obiwanjacobi/zalt2/chats/smart IDE module.md

> This refers to `Zalt\Under Construction\IDE v0.2\readme.md`

This is a **really well-thought-out design**. You've clearly put significant effort into abstracting away the complexity while maintaining practical performance. Let me give you some detailed feedback.

## Overall Architecture

**Strengths:**
- **Clean abstraction** — the Z80 program never deals with IDE timing, sectors, or cluster chains. It just says "read file X" or "write Y bytes"
- **Efficient pipelining** — prefetching the next block while the Z80 processes the current one is smart
- **DMA-driven** — the MCU takes the bus only when needed, minimizing Z80 stalls
- **Flexible addressing** — ContentOffset and ContentLength let you handle partial file reads/writes elegantly
- **Interleaving support** — multiple command blocks means you can juggle several operations

**The design handles real constraints well** — the 4kB MCU buffer limit is acknowledged, and you've built the block-based protocol around it.

---

## Detailed Observations

### Register Design

Your register set is minimal and clean. A few thoughts:

**Buffer Address and Command Buffer Address:**
- Good that you require the Z80 raw address — this avoids the MCU needing to understand the MMU
- One edge case: what if the Z80 program accidentally sets Buffer Address to overlap with Command Buffer Address? Should the MCU validate this, or is it the Z80 program's responsibility?

**BlockIndex as a trigger:**
- Elegant — writing BlockIndex both specifies which block and triggers the operation
- **Question:** Can the Z80 write BlockIndex=0 multiple times to restart a command, or does that require zeroing the command block first?

**Status register:**
- Good that it captures the status at the moment the MCU releases the bus (so the Z80 program knows if more data is coming)
- **Suggestion:** Consider whether you need a separate "interrupt enable" bit or if Status register writes are just for clearing/acknowledging interrupts

---

### Command Structure

**The variable-length MetaRecord is clever but risky:**

```c
struct MetaRecord {
    MetaFlags   Flags;      // 1 byte
    uint32_t    ContentLength;
    uint16_t    Date;
    uint16_t    Time;
    char        Location[1+];   // variable!
}
```

**Potential issues:**
- **Alignment:** If you're reading MetaRecords sequentially from a buffer, how do you know where one ends and the next begins? You have to parse the Location string to find the null terminator. This works, but it means the Z80 program can't use a fixed stride to iterate.
- **Buffer boundary problem:** What if a MetaRecord is split across two block transfers? For example, the filename is 50 bytes and the buffer ends in the middle of it? You mention "it will always contain a number of complete structures," but how does the MCU ensure this? Does it back off and reduce StreamLength if the next record won't fit?

**Suggestion:** Consider a two-pass approach for large directories:
1. First pass: MCU counts how many complete MetaRecords fit in the buffer
2. Second pass: MCU fills the buffer with exactly that many complete records
3. Z80 program iterates through them, then requests the next block

---

### ContentOffset and ContentLength

**This is powerful but adds complexity:**

- **For reads:** Makes sense — "give me bytes 1000-2000 of this file"
- **For writes:** What does it mean? "Write this block starting at offset 1000 in the file"? Or "only write the bytes that correspond to the original 1000-2000 range"?
- **For meta operations:** You say "usually not very useful" — but what if someone wants to skip the first 10 files in a directory listing? Does ContentOffset work there?

**Suggestion:** Be explicit about whether ContentOffset applies to:
- File data only (Read/Write commands)
- Meta streams (Find/ReadMeta)
- Or both, with different semantics

---

### The Direct Flag

> The `Direct` flag on any command indicates that the operation is to use the data from the Z80 memory directly and not copy it to the IDE controller's internal memory first.

**This is interesting but I'm not sure I understand it:**
- For **Read commands**, there's no "copy to internal memory first" — data comes from disk. So Direct doesn't apply?
- For **Write commands**, Direct would mean: MCU reads from Z80 memory and writes directly to IDE without buffering. But then the Z80 can't modify the buffer while the write is in progress. Is that the trade-off?
- For **Meta commands**, what does Direct mean?

**Suggestion:** Clarify or remove this flag if it's not essential. It adds complexity without obvious benefit.

---

### Error Handling

**You mention:**
> It is also an error when the `BlockIndex` written to the IO register of the IDE controller is outside the range of the `ContentLength` and `ContentOffset` specified in the command parameter block.

**But how does the Z80 program know what the valid range is?**
- If ContentLength = 1000 bytes and BufferLength = 512 bytes, then BlockIndex can be 0 or 1 (covering bytes 0-511 and 512-999)
- But the Z80 program has to calculate this. Should the MCU provide a hint (like "max block index for this command")?

**Also missing:**
- What errors can occur? (Disk read error, file not found, out of space, etc.)
- How are they reported? (Status field? Additional error code?)
- Can the Z80 program distinguish between "file doesn't exist" and "disk I/O error"?

---

### Sequential Flag and Prefetching

**This is a nice optimization:**
> This allows the IDE controller to prefetch data for the next block while the Z80 program is processing the current block.

**But there's a subtle issue:**
- If the Z80 program sets Sequential and then writes BlockIndex=5 (skipping ahead), what happens? Does the MCU:
  - Abort the prefetch and seek to block 5?
  - Treat this as an error?
  - Ignore the Sequential flag retroactively?

**Suggestion:** Either forbid random access when Sequential is set, or clarify what happens.

---

### Write Command Flow

**You describe:**
> The Z80 program can fill its data buffer in memory in the meantime, to prepare for the next write cycle.

**This assumes:**
- The Z80 program knows when to start filling the next block (after the interrupt fires)
- The Z80 program has enough time to fill the entire buffer before the MCU finishes writing the current block to disk

**What if the Z80 program is slow and hasn't finished filling the buffer when the MCU finishes the disk write and generates an interrupt?** Does the MCU:
- Wait for the Z80 to signal BlockIndex again?
- Time out and generate an error?

This is probably fine in practice, but it's worth documenting.

---

### File Path Syntax

**You support:**
```
/MyFolder/MyFile.dat
/**/*.txt
/MyFile.dat
```

**Questions:**
- Does `/**/*.txt` find files at any depth, or just one level deep?
- What about `/**/subfolder/file.txt` — does that work?
- Can the Z80 program use relative paths, or always absolute?
- What's the max path length? (Relevant for command block size)

---

## Practical Suggestions

### 1. **Command Block Size**

You don't specify the fixed size of the CommandParameters structure. This is important because:
- It determines how much space is "reserved" in Z80 memory
- It affects the minimum size of the command buffer

**Suggestion:** Define this explicitly. Something like:
```c
struct CommandParameters {
    uint8_t     Command;
    uint8_t     Status;
    uint16_t    ContentLength;
    uint16_t    ContentOffset;
    uint16_t    Location;        // pointer to string
    uint16_t    StreamLength;
    uint16_t    StreamOffset;
    uint8_t     Filler[N];       // reserved for MCU state
}
// Total: fixed size, e.g., 64 bytes or 128 bytes
```

### 2. **Interrupt Vector Register**

You mention:
> Interrupt Vector | IM0 RST instruction or IM2 interrupt vector

**This is powerful but unusual.** Most systems pick one mode (IM0 or IM2) at boot. Are you allowing the Z80 program to switch modes dynamically? If so:
- What happens if an interrupt fires while the Z80 is reconfiguring?
- Does the MCU need to disable interrupts during the switch?

**Suggestion:** Either lock the mode at boot, or add a "lock" bit to prevent runtime changes.

### 3. **RAM Disk Support**

You mention:
> For a (potential) RAM disk, we need extra registers that point to the RAM disk buffer (in Z80 memory) and defines its length.

**This is good future-proofing.** When you implement it:
- RAM disk operations should use the same command protocol
- The MCU needs to distinguish between "IDE disk" and "RAM disk" commands (maybe via a register, or by path prefix like `ram:/file.txt`)

### 4. **Meta Stream Iteration**

For large directories, the Z80 program will need to:
1. Issue ReadMeta for the root
2. Parse the MetaRecords
3. Write BlockIndex to get the next batch
4. Repeat until Flags=None

**Suggestion:** Document a code example showing how to iterate through a large directory. It'll help catch design issues early.

---

## What's Missing?

### File Creation / Truncation

- **Write** command creates a file if it doesn't exist, but what if you want to truncate an existing file?
- What if you want to append to a file (ContentOffset = file size)?

### Timestamps

- MetaRecord includes Date and Time, but can the Z80 program set them when creating files?
- Or are they always system time?

### Permissions / Attributes

- MetaFlags includes Protected and Hidden, but can the Z80 program set these?

### Multiple Drives / Partitions

- You note "No provision for Volumes, Partitions, (un)mounting yet"
- Future consideration: how will paths look? (`drive1:/file.txt`? or a separate register?)

---

## Overall Assessment

**This is a solid, practical design.** The abstraction level is right — high enough to hide IDE complexity, low enough to give the Z80 program fine-grained control. The block-based protocol with prefetching should perform well even on a Z80 running at a few MHz.

**Main recommendations:**
1. Clarify error codes and how they're reported
2. Define the exact size and layout of CommandParameters
3. Document the behavior of ContentOffset/ContentLength for each command type
4. Provide a worked example of directory iteration
5. Reconsider or clarify the Direct flag

Are you planning to implement this soon, or still in the design phase? If you're coding it up, I'd be curious to hear how the Z80 side of the driver turns out — the protocol is clean, but the Z80 assembly to manage all this state will be interesting.
